tjhorner/bizcard/firmware/src/notes.h

#include <Arduino.h>
#include <Adafruit_NeoPixel.h>
#include "pins.h"

namespace notes {

struct NoteDefinition
{
  unsigned int frequency;
  double duration;
  double delayAfter;
  bool pause; // should pause at this note
};

const NoteDefinition notes[] = {
    {784, 250, 250, false},
    {740, 250, 250, false},
    {659, 250, 250, false},
    {659, 250, 250, false},
    {740, 250, 0, true},
    {440, 250, 250, false},
    {784, 250, 250, false},
    {740, 250, 250, false},
    {659, 250, 250, false},
    {659, 500, 500, false},
    {740, 250, 750, false},
    {587, 500, 500, false},
    {659, 250, 250, false},
    {440, 500, 0, true},
    {440, 250, 250, false},
    {659, 500, 500, false},
    {740, 250, 250, false},
    {784, 750, 750, false},
    {659, 250, 250, false},
    {554, 500, 500, false},
    {587, 750, 750, false},
    {659, 500, 500, false},
    {440, 250, 250, false},
    {440, 500, 500, false},
    {740, 500, 0, true},
    {784, 250, 250, false},
    {740, 250, 250, false},
    {659, 250, 250, false},
    {659, 250, 250, false},
    {740, 250, 0, true},
    {440, 250, 250, false},
    {784, 250, 250, false},
    {740, 250, 250, false},
    {659, 250, 250, false},
    {659, 500, 750, false},
    {740, 250, 250, false},
    {587, 500, 750, false},
    {659, 250, 250, false},
    {440, 500, 0, true},
    {659, 500, 500, false},
    {740, 250, 250, false},
    {784, 750, 750, false},
    {659, 250, 250, false},
    {554, 750, 750, false},
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
    {659, 250, 250, false},
    {740, 250, 250, false},
    {740, 500, 1500, false},
    {784, 250, 250, false},
    {880, 250, 250, false},
    {880, 500, 1500, false},
    {784, 250, 250, false},
    {740, 250, 250, false},
    {740, 500, 0, true}};

void setup();
void playNextSegment();

}
